AdlerFarHorizons/CutDownSystem/software/CutDownBase/CutDownBase.ino

#include <SoftwareSerial.h>
#include <math.h>
#include "TinyGPS.h"
#include <SD.h>

#define XBEE_SLEEP 7
#define GPS_RX 5 //3 
#define GPS_TX 6 //4
#define LOG_FILE_NAME "baselog.txt"
const int chipSelectSD = 4;
boolean isLogging;

TinyGPS gps;
SoftwareSerial nss(GPS_TX, GPS_RX); // nss(Arduino Rx, Arduino Tx) = nss(GPS Tx, GPS Rx)
unsigned long startTime;
unsigned long endTime;
int flightTime;
double cutPercent = 0.9; //The percent of the flight that can go by before the BaseModule is
                      //authorized to cut the balloon.
double maxAltitude = 0;
double maxRadius = 0;
double center_lat = 0;
double center_lon = 0;
const double RADIUS = 3963.1676; //radius of the earth in miles
boolean isTimeCutdown = false; //boolean to store whether the BaseModule has sent a timer cutdown command or not
boolean isAltCutdown = false; //boolean to store whether the BaseModule has sent a timer cutdown command or not
boolean isRangeCutdown = false; //boolean to store whether the BaseModule has sent a timer cutdown command or not
boolean gpsValid = false;

int c;
long alt, lat, lon;
double scaledLat, scaledLon;
unsigned long date, time, age;
unsigned long loopStart;

void setup()
{
  Serial.begin(9600);
  Serial.println(freeRam());
  Serial.flush();
  nss.begin(4800);
  nss.flush();
  pinMode( 10, OUTPUT );
  pinMode(XBEE_SLEEP, OUTPUT);
  digitalWrite(XBEE_SLEEP, LOW); delay(10);  
  
  waitForTimeStart();
  
  // see if the card is present and can be initialized:
  if (!SD.begin(chipSelectSD))
  {
    Serial.println("");
    Serial.println( "Base: SD failed, no logging" );
    Serial.println( "" );
    isLogging = false;
  } else
  {
    Serial.println( "Base: SD initialized" );
    // Check if dataFile can be created/opened and write header
    File dataFile = SD.open(LOG_FILE_NAME, FILE_WRITE);
    if (dataFile)
    {
      Serial.println("Base: File open, log enabled.");
      isLogging = true;
      dataFile.println("");
      dataFile.println("");
      dataFile.println("Cut Down Base Log");
      dataFile.println("");
      dataFile.print("Max(min):"); dataFile.println(flightTime);
      dataFile.print("Start(ms):"); dataFile.println(startTime);
      dataFile.print("End(ms):"); dataFile.println(endTime);
      dataFile.print("Alt(ft):"); dataFile.println(maxAltitude*3.2804); //convert to feet
      dataFile.print("Range(mi):"); dataFile.print(maxRadius); dataFile.print(" from:"); dataFile.print(center_lat,6); dataFile.print(","); dataFile.println(center_lon,6);
      dataFile.println("ms\tddmmyy\thhmmss..\tlat\t\tlon\t\talt(m)");
      dataFile.close();
    } else
    {
      Serial.println( "Base: No File. Log disabled." );
      isLogging = false;
    } 
  }

  //send xbee to sleep and move to loop function
  digitalWrite(XBEE_SLEEP, HIGH); delay(10); 
  
}

void waitForTimeStart()
{
  boolean timeReceived = false;
  while(!timeReceived)
  {
    if (Serial.available() > 0)
    {
      int incomingByte = Serial.read();
      if (incomingByte == 'X')
      {
        flightTime = Serial.parseInt();
        maxAltitude = Serial.parseFloat();
        maxAltitude /= 3.2804; //convert to meters
        maxRadius = Serial.parseFloat();
        center_lat = Serial.parseFloat();
        center_lon = Serial.parseFloat();
        
        startTime = millis();
        endTime = startTime + (cutPercent*flightTime*60*1000);
        timeReceived = true;
        // The following only print when testing through USB
        Serial.println("ms\tddmmyy\thhmmss..\tlat\t\tlon\t\talt(m)\tRAM");
        Serial.print("\nMax(min):"); Serial.println(flightTime);
        Serial.print("Start(ms):"); Serial.println(startTime);
        Serial.print("End(ms):"); Serial.println(endTime);
        Serial.print("Alt(ft): "); Serial.println(maxAltitude*3.2804); //convert to feet
        Serial.print("Range(mi):"); Serial.print(maxRadius); Serial.print(" from:"); Serial.print(center_lat); Serial.print(","); Serial.println(center_lon);
        Serial.flush();
      }
    }
    delay(1);
  }  
}

void loop() 
{
  loopStart = millis(); // Used for optional loop time reporting.

  // Check if endTime has arrived
  if (millis() >= endTime ) 
  { 
    if (!isTimeCutdown && isLogging) //if logging is enabled, log some stuff
    {
      File dataFile = SD.open(LOG_FILE_NAME, FILE_WRITE);
      if ( dataFile )
      {
        dataFile.print( millis() ); dataFile.println(" *** Time cutdown ***");
        dataFile.close();
      }
      cutdown();
      isTimeCutdown = true; // Run only once
    }
  }
  
  //check if altitude is greater than maximum altitude
  if ( gpsValid && ( (double)alt > (double)maxAltitude ) )
  {
    if (!isAltCutdown && isLogging)
    {
      File dataFile = SD.open(LOG_FILE_NAME, FILE_WRITE);
      if (dataFile)
      {
        dataFile.print( millis() ); dataFile.println(" *** Altitude cutdown ***");
        dataFile.close();
      }
      cutdown(); //Suppressed for now
      isAltCutdown = true; //run only once
    }
  }
  
  double d = distanceBetweenTwoPoints(scaledLat, scaledLon, center_lat, center_lon);  
  if ( gpsValid && ( d > maxRadius ) )
  {
    if (!isRangeCutdown && isLogging)
    {
      File dataFile = SD.open(LOG_FILE_NAME, FILE_WRITE);
      if (dataFile)
      {
        dataFile.print( millis() ); dataFile.println(" *** Range cutdown ***");
        dataFile.close();
      }
      cutdown(); // Actual cutdown by altitude is suppressed for now.
      isRangeCutdown = true; //run only once
    }
  }
  //Check the GPS
  gpsValid = false;
  while (nss.available() > 0)
  {
    c = nss.read();
    if (gps.encode(c))
    {
      //get data from the gps object
      alt = gps.altitude()/100; //altitude() returns in centimeters. all of the conversions were previously done in meters. dividing by 100 converts cm's to m's.
      // Uncomment to give simulated altitude.
      //alt = 300 + ( 6*(millis()-startTime) )/1000;
      gps.get_position(&lat, &lon);
      scaledLat = lat / pow(10,6); //divide by 10^6
      scaledLon = lon / pow(10,6); //divide by 10^6
      gps.get_datetime(&date, &time, &age);
      gpsValid = age < 500;
      
      //print all of the data, tab delimited
      //Uncomment for remote terminal GPS output
      //digitalWrite(XBEE_SLEEP, LOW); delay(20);  
      Serial.print(millis()); Serial.print("\t");
      Serial.print(date); Serial.print("\t");
      Serial.print(time); Serial.print("\t");
      Serial.print(scaledLat,6); Serial.print("\t");
      Serial.print(scaledLon,6); Serial.print("\t");
      Serial.print(alt);Serial.print("\t");
      Serial.println(freeRam());
      Serial.flush();
      //Uncomment for remote terminal GPS output
      //digitalWrite(XBEE_SLEEP, HIGH);
      // Log data to file if enabled and GPS is valid
      if ( isLogging && gpsValid )
      {
        File dataFile = SD.open(LOG_FILE_NAME, FILE_WRITE);
        
        if (dataFile)
        {
          dataFile.print(millis()); dataFile.print("\t");
          dataFile.print(date); dataFile.print("\t");
          dataFile.print(time); dataFile.print("\t");
          dataFile.print(scaledLat,6); dataFile.print("\t");
          dataFile.print(scaledLon,6); dataFile.print("\t");
          dataFile.println(alt);
          dataFile.close();
         }
      }
    }
    
    // The following delay should be 10/BaudRate to allow time
    // for the next character to be ready so it stays in this loop
    // until the NMEA messages have a chance to be fully received.
    delay(2);
  }
  
  // Uncomment following line for loop time report.
  //Serial.print("loop:");Serial.println( millis() - loopStart );
}

double distanceBetweenTwoPoints(double lat1, double lon1, double lat2, double lon2)
{
  double dLat = deg2rad(lat2-lat1);
  double dLon = deg2rad(lon2-lon1);
  double latOne = deg2rad(lat1);
  double latTwo = deg2rad(lat2);
  
  double a = sin(dLat/2.0)*sin(dLat/2.0) +
             sin(dLon/2.0)*sin(dLon/2.0) * cos(lat1)*cos(lat2);
  double c = 2.0 * atan2(sqrt(a), sqrt(1-a));
  double d_miles = RADIUS * c;
  return d_miles;
}

void cutdown()
{
  // Wake up XBEE
  digitalWrite(XBEE_SLEEP, LOW); delay(20);
  
  //Send 175 'C's with 20ms between them for > 3.5sec
  for (int i = 0; i < 175; i++)
  {
    Serial.print('C');
    delay(20);
  }
  Serial.println("");
  Serial.flush();
  
  //put the xbee back to sleep
  digitalWrite(XBEE_SLEEP, HIGH); delay(1);
}
double deg2rad(double degree)
{
  return degree * (PI/180.0);
}

int freeRam() 
{
  extern int __heap_start, *__brkval; 
  int v; 
  return (int) &v - (__brkval == 0 ? (int) &__heap_start : (int) __brkval); 
}
